squirrelmedia/X-TRACK/Software/X-Track/USER/App/Config/Config.h

/*
 * MIT License
 * Copyright (c) 2021 _VIFEXTech
 *
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
 * THE SOFTWARE IS PROVIDED "AS IS", WITHOUT WARRANTY OF ANY KIND, EXPRESS OR
 * IMPLIED, INCLUDING BUT NOT LIMITED TO THE WARRANTIES OF MERCHANTABILITY,
 * FITNESS FOR A PARTICULAR PURPOSE AND NONINFRINGEMENT. IN NO EVENT SHALL THE
 * AUTHORS OR COPYRIGHT HOLDERS BE LIABLE FOR ANY CLAIM, DAMAGES OR OTHER
 * LIABILITY, WHETHER IN AN ACTION OF CONTRACT, TORT OR OTHERWISE, ARISING FROM,
 * OUT OF OR IN CONNECTION WITH THE SOFTWARE OR THE USE OR OTHER DEALINGS IN THE
 * SOFTWARE.
 */
#ifndef __CONFIG_H
#define __CONFIG_H

/*=========================
   Application configuration
 *=========================*/

#define CONFIG_SYSTEM_SAVE_FILE_PATH          "/SystemSave.json"
#define CONFIG_SYSTEM_SAVE_FILE_BACKUP_PATH   "/.SystemSaveBackup.json"
#define CONFIG_SYSTEM_LANGUAGE_DEFAULT        "en-GB"
#define CONFIG_SYSTEM_TIME_ZONE_DEFAULT       8    // GMT+ 8
#define CONFIG_SYSTEM_SOUND_ENABLE_DEFAULT    true

#define CONFIG_WEIGHT_DEFAULT                 65   // kg

#ifdef ARDUINO
#  define CONFIG_GPS_REFR_PERIOD              1000 // ms
#else
#  define CONFIG_GPS_REFR_PERIOD              10 // ms
#endif

#define CONFIG_GPS_LONGITUDE_DEFAULT          116.391332f
#define CONFIG_GPS_LATITUDE_DEFAULT           39.907415f

#define CONFIG_TRACK_FILTER_OFFSET_THRESHOLD  2 // pixel
#define CONFIG_TRACK_RECORD_FILE_DIR_NAME     "Track"

#define CONFIG_MAP_USE_WGS84_DEFAULT          false
#define CONFIG_MAP_DIR_PATH_DEFAULT           "/MAP"

#define CONFIG_MAP_EXT_NAME_DEFAULT           "bin"

#ifndef CONFIG_MAP_IMG_PNG_ENABLE
#  define CONFIG_MAP_IMG_PNG_ENABLE           0
#endif

#define CONFIG_ARROW_THEME_DEFAULT            "default"

#define CONFIG_LIVE_MAP_LEVEL_DEFAULT         16

#define CONFIG_LIVE_MAP_DEBUG_ENABLE          0
#if CONFIG_LIVE_MAP_DEBUG_ENABLE
#  define CONFIG_LIVE_MAP_VIEW_WIDTH          240
#  define CONFIG_LIVE_MAP_VIEW_HEIGHT         240
#else
#  define CONFIG_LIVE_MAP_VIEW_WIDTH          LV_HOR_RES
#  define CONFIG_LIVE_MAP_VIEW_HEIGHT         LV_VER_RES
#endif

#define CONFIG_MONKEY_TEST_ENABLE             0
#if CONFIG_MONKEY_TEST_ENABLE
#  define CONFIG_MONKEY_INDEV_TYPE            LV_INDEV_TYPE_ENCODER
#  define CONFIG_MONKEY_PERIOD_MIN            10
#  define CONFIG_MONKEY_PERIOD_MAX            100
#  define CONFIG_MONKEY_INPUT_RANGE_MIN       -5
#  define CONFIG_MONKEY_INPUT_RANGE_MAX       5
#endif

#endif
