squirrelmedia/X-TRACK/Software/X-Track/MDK-ARM_F403A/Platform/Core/HardwareSerial.h

/*
 * MIT License
 * Copyright (c) 2019 _VIFEXTech
 *
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
 * THE SOFTWARE IS PROVIDED "AS IS", WITHOUT WARRANTY OF ANY KIND, EXPRESS OR
 * IMPLIED, INCLUDING BUT NOT LIMITED TO THE WARRANTIES OF MERCHANTABILITY,
 * FITNESS FOR A PARTICULAR PURPOSE AND NONINFRINGEMENT. IN NO EVENT SHALL THE
 * AUTHORS OR COPYRIGHT HOLDERS BE LIABLE FOR ANY CLAIM, DAMAGES OR OTHER
 * LIABILITY, WHETHER IN AN ACTION OF CONTRACT, TORT OR OTHERWISE, ARISING FROM,
 * OUT OF OR IN CONNECTION WITH THE SOFTWARE OR THE USE OR OTHER DEALINGS IN THE
 * SOFTWARE.
 */
#ifndef __HardwareSerial_h
#define __HardwareSerial_h

#include "Arduino.h"
#include "Print.h"
#include "Stream.h"

typedef enum
{
    SERIAL_8N1 = USART_WordLength_8b | USART_Parity_No | (USART_StopBits_1 >> 8),
    SERIAL_8N2 = USART_WordLength_8b | USART_Parity_No | (USART_StopBits_2 >> 8),
    SERIAL_8E1 = USART_WordLength_8b | USART_Parity_Even | (USART_StopBits_1 >> 8),
    SERIAL_8E2 = USART_WordLength_8b | USART_Parity_Even | (USART_StopBits_2 >> 8),
    SERIAL_8O1 = USART_WordLength_8b | USART_Parity_Odd | (USART_StopBits_1 >> 8),
    SERIAL_8O2 = USART_WordLength_8b | USART_Parity_Odd | (USART_StopBits_2 >> 8),
    SERIAL_8N0_5 = USART_WordLength_8b | USART_Parity_No | (USART_StopBits_0_5 >> 8),
    SERIAL_8N1_5 = USART_WordLength_8b | USART_Parity_No | (USART_StopBits_1_5 >> 8),
    SERIAL_8E0_5 = USART_WordLength_8b | USART_Parity_Even | (USART_StopBits_0_5 >> 8),
    SERIAL_8E1_5 = USART_WordLength_8b | USART_Parity_Even | (USART_StopBits_1_5 >> 8),
    SERIAL_8O0_5 = USART_WordLength_8b | USART_Parity_Odd | (USART_StopBits_0_5 >> 8),
    SERIAL_8O1_5 = USART_WordLength_8b | USART_Parity_Odd | (USART_StopBits_1_5 >> 8),

    SERIAL_9N1 = USART_WordLength_9b | USART_Parity_No | (USART_StopBits_1 >> 8),
    SERIAL_9N2 = USART_WordLength_9b | USART_Parity_No | (USART_StopBits_2 >> 8),
    SERIAL_9E1 = USART_WordLength_9b | USART_Parity_Even | (USART_StopBits_1 >> 8),
    SERIAL_9E2 = USART_WordLength_9b | USART_Parity_Even | (USART_StopBits_2 >> 8),
    SERIAL_9O1 = USART_WordLength_9b | USART_Parity_Odd | (USART_StopBits_1 >> 8),
    SERIAL_9O2 = USART_WordLength_9b | USART_Parity_Odd | (USART_StopBits_2 >> 8),
    SERIAL_9N0_5 = USART_WordLength_9b | USART_Parity_No | (USART_StopBits_0_5 >> 8),
    SERIAL_9N1_5 = USART_WordLength_9b | USART_Parity_No | (USART_StopBits_1_5 >> 8),
    SERIAL_9E0_5 = USART_WordLength_9b | USART_Parity_Even | (USART_StopBits_0_5 >> 8),
    SERIAL_9E1_5 = USART_WordLength_9b | USART_Parity_Even | (USART_StopBits_1_5 >> 8),
    SERIAL_9O0_5 = USART_WordLength_9b | USART_Parity_Odd | (USART_StopBits_0_5 >> 8),
    SERIAL_9O1_5 = USART_WordLength_9b | USART_Parity_Odd | (USART_StopBits_1_5 >> 8),
} SERIAL_Config_t;

class HardwareSerial : public Stream
{
    typedef void(*CallbackFunction_t)(HardwareSerial* serial);

public:
    HardwareSerial(USART_Type* usart);

    USART_Type* getUSART()
    {
        return _USARTx;
    }

    void begin(
        uint32_t baudRate,
        SERIAL_Config_t config = SERIAL_CONFIG_DEFAULT,
        uint8_t preemptionPriority = SERIAL_PREEMPTIONPRIORITY_DEFAULT,
        uint8_t subPriority = SERIAL_SUBPRIORITY_DEFAULT
    );
    void end(void);
    void attachInterrupt(CallbackFunction_t func);
    virtual int available(void);
    virtual int peek(void);
    virtual int read(void);
    virtual void flush(void);

    virtual size_t write(uint8_t n);
    inline size_t write(unsigned long n)
    {
        return write((uint8_t)n);
    }
    inline size_t write(long n)
    {
        return write((uint8_t)n);
    }
    inline size_t write(unsigned int n)
    {
        return write((uint8_t)n);
    }
    inline size_t write(int n)
    {
        return write((uint8_t)n);
    }
    using Print::write; // pull in write(str) and write(buf, size) from Print
    operator bool()
    {
        return true;
    }

    void IRQHandler();

private:
    USART_Type* _USARTx;
    CallbackFunction_t _callbackFunction;
    volatile uint16_t _rxBufferHead;
    volatile uint16_t _rxBufferTail;
    uint8_t _rxBuffer[SERIAL_RX_BUFFER_SIZE];
};

#if SERIAL_1_ENABLE
extern HardwareSerial Serial;
#endif

#if SERIAL_2_ENABLE
extern HardwareSerial Serial2;
#endif

#if SERIAL_3_ENABLE
extern HardwareSerial Serial3;
#endif

#endif
