squirrelmedia/X-TRACK/Software/X-Track/Linux/mouse_cursor_icon.c

#include "lvgl/lvgl.h"

const uint8_t mouse_cursor_icon_map[] = {
#if LV_COLOR_DEPTH == 1 || LV_COLOR_DEPTH == 8
    /*Pixel format: Alpha 8 bit, Red: 3 bit, Green: 3 bit, Blue: 2 bit*/
    0x24, 0xb8, 0x24, 0xc8, 0x00, 0x13, 0x00, 0x00, 0x00, 0x03, 0x00, 0x00, 0x00, 0x00, 0x00, 0x00, 0x00, 0x00, 0x00, 0x00, 0x00, 0x00, 0x00, 0x00, 0x00, 0x00, 0x00, 0x00,
    0x49, 0xcc, 0xdb, 0xff, 0x49, 0xcc, 0x00, 0x24, 0x00, 0x00, 0x00, 0x00, 0x00, 0x00, 0x00, 0x00, 0x00, 0x00, 0x00, 0x00, 0x00, 0x00, 0x00, 0x00, 0x00, 0x00, 0x00, 0x00,
    0x49, 0xc8, 0xff, 0xff, 0xff, 0xff, 0x49, 0xe0, 0x00, 0x3b, 0x00, 0x00, 0x00, 0x00, 0x00, 0x00, 0x00, 0x00, 0x00, 0x00, 0x00, 0x00, 0x00, 0x00, 0x00, 0x00, 0x00, 0x00,
    0x49, 0xcb, 0xff, 0xff, 0xff, 0xfc, 0xff, 0xff, 0x6d, 0xf3, 0x00, 0x4f, 0x00, 0x00, 0x00, 0x00, 0x00, 0x00, 0x00, 0x00, 0x00, 0x00, 0x00, 0x00, 0x00, 0x00, 0x00, 0x00,
    0x49, 0xcb, 0xff, 0xff, 0xff, 0xff, 0xff, 0xff, 0xff, 0xff, 0x92, 0xff, 0x00, 0x73, 0x00, 0x00, 0x00, 0x00, 0x00, 0x03, 0x00, 0x00, 0x00, 0x00, 0x00, 0x00, 0x00, 0x00,
    0x49, 0xcb, 0xff, 0xff, 0xff, 0xff, 0xff, 0xff, 0xff, 0xff, 0xff, 0xff, 0x92, 0xff, 0x00, 0x90, 0x00, 0x00, 0x00, 0x00, 0xb6, 0x00, 0x00, 0x00, 0x00, 0x00, 0x00, 0x00,
    0x49, 0xcb, 0xff, 0xff, 0xff, 0xff, 0xff, 0xff, 0xff, 0xff, 0xff, 0xff, 0xff, 0xff, 0xb7, 0xff, 0x24, 0xab, 0x00, 0x04, 0x00, 0x00, 0x00, 0x00, 0x00, 0x00, 0x00, 0x00,
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
#endif
};

lv_img_dsc_t mouse_cursor_icon = {
    .header.always_zero = 0,
    .header.w = 14,
    .header.h = 20,
    .data_size = 280 * LV_IMG_PX_SIZE_ALPHA_BYTE,
    .header.cf = LV_IMG_CF_TRUE_COLOR_ALPHA,
    .data = mouse_cursor_icon_map,
};
