squirrelmedia/X-TRACK/Software/X-Track/MDK-ARM_F403A/Platform/Core/SPI.h

/*
 * MIT License
 * Copyright (c) 2017 - 2022 _VIFEXTech
 *
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
 * THE SOFTWARE IS PROVIDED "AS IS", WITHOUT WARRANTY OF ANY KIND, EXPRESS OR
 * IMPLIED, INCLUDING BUT NOT LIMITED TO THE WARRANTIES OF MERCHANTABILITY,
 * FITNESS FOR A PARTICULAR PURPOSE AND NONINFRINGEMENT. IN NO EVENT SHALL THE
 * AUTHORS OR COPYRIGHT HOLDERS BE LIABLE FOR ANY CLAIM, DAMAGES OR OTHER
 * LIABILITY, WHETHER IN AN ACTION OF CONTRACT, TORT OR OTHERWISE, ARISING FROM,
 * OUT OF OR IN CONNECTION WITH THE SOFTWARE OR THE USE OR OTHER DEALINGS IN THE
 * SOFTWARE.
 */
#ifndef __SPI_H
#define __SPI_H

#include "Arduino.h"

#ifndef LSBFIRST
#  define LSBFIRST 0
#endif
#ifndef MSBFIRST
#  define MSBFIRST 1
#endif

#if SPI_CLASS_PIN_DEFINE_ENABLE
#  define SS      PA4
#  define SCK     PA5
#  define MISO    PA6
#  define MOSI    PA7
#endif

#define DATA_SIZE_8BIT  SPI_FRAMESIZE_8BIT
#define DATA_SIZE_16BIT SPI_FRAMESIZE_16BIT

#define SPI_I2S_GET_FLAG(spix, SPI_I2S_FLAG) (spix->STS & SPI_I2S_FLAG)
#define SPI_I2S_RXDATA(spix)                 (spix->DT)
#define SPI_I2S_RXDATA_VOLATILE(spix)        volatile uint16_t vn = SPI_I2S_RXDATA(spix)
#define SPI_I2S_TXDATA(spix, data)           (spix->DT = (data))
#define SPI_I2S_WAIT_RX(spix)                do{ while (!SPI_I2S_GET_FLAG(spix, SPI_I2S_FLAG_RNE));  } while(0)
#define SPI_I2S_WAIT_TX(spix)                do{ while (!SPI_I2S_GET_FLAG(spix, SPI_STS_TE));        } while(0)
#define SPI_I2S_WAIT_BUSY(spix)              do{ while (SPI_I2S_GET_FLAG(spix,  SPI_I2S_FLAG_BUSY)); } while(0)

typedef enum
{
    SPI_MODE0,
    SPI_MODE1,
    SPI_MODE2,
    SPI_MODE3
} SPI_MODE_TypeDef;

typedef enum
{
    SPI_STATE_IDLE,
    SPI_STATE_READY,
    SPI_STATE_RECEIVE,
    SPI_STATE_TRANSMIT,
    SPI_STATE_TRANSFER
} spi_mode_t;

class SPISettings
{
public:
    SPISettings(uint32_t clock, uint16_t bitOrder, uint8_t dataMode)
    {
        init_AlwaysInline(clock, bitOrder, dataMode, DATA_SIZE_8BIT);
    }
    SPISettings(uint32_t clock, uint16_t bitOrder, uint8_t dataMode, uint32_t dataSize)
    {
        init_AlwaysInline(clock, bitOrder, dataMode, dataSize);
    }
    SPISettings(uint32_t clock)
    {
        init_AlwaysInline(clock, MSBFIRST, SPI_MODE0, DATA_SIZE_8BIT);
    }
    SPISettings()
    {
        init_AlwaysInline(4000000, MSBFIRST, SPI_MODE0, DATA_SIZE_8BIT);
    }
private:
    void init_MightInline(uint32_t clock, uint16_t bitOrder, uint8_t dataMode, uint32_t dataSize)
    {
        init_AlwaysInline(clock, bitOrder, dataMode, dataSize);
    }
    void init_AlwaysInline(uint32_t clock, uint16_t bitOrder, uint8_t dataMode, uint32_t dataSize) __attribute__((__always_inline__))
    {
        this->clock = clock;
        this->bitOrder = bitOrder;
        this->dataMode = dataMode;
        this->dataSize = dataSize;
    }
    uint32_t clock;
    uint32_t dataSize;
    uint16_t bitOrder;
    uint8_t dataMode;

    friend class SPIClass;
};

class SPIClass
{
public:
    SPIClass(SPI_Type* spix);

    SPI_Type* getSPI()
    {
        return SPIx;
    }

    void SPI_Settings(
        uint16_t SPI_Mode_x,
        uint16_t SPI_DataSize_x,
        uint16_t SPI_MODEx,
        uint16_t SPI_NSS_x,
        uint16_t SPI_BaudRatePrescaler_x,
        uint16_t SPI_FirstBit_x
    );
    void begin(void);
    void begin(uint32_t clock, uint16_t dataOrder, uint16_t dataMode);
    void begin(SPISettings settings);
    void beginSlave(uint32_t bitOrder, uint32_t mode);
    void beginSlave(void);
    void beginTransactionSlave(void);
    void beginTransaction(SPISettings settings);

    void endTransaction(void);
    void end(void);

    void setClock(uint32_t clock);
    void setClockDivider(uint32_t Div);
    void setBitOrder(uint16_t bitOrder);
    void setDataMode(uint8_t dataMode);
    void setDataSize(uint16_t datasize);

    uint16_t read(void);
    void read(uint8_t* buffer, uint32_t length);
    void write(uint16_t data);
    void write(uint16_t data, uint32_t n);
    void write(const uint8_t* data, uint32_t length);
    void write(const uint16_t* data, uint32_t length);
    uint8_t transfer(uint8_t data) const;
    uint16_t transfer16(uint16_t data) const;
    uint8_t send(uint8_t data);
    uint8_t send(uint8_t* data, uint32_t length);
    uint8_t recv(void);

private:
    SPI_Type* SPIx;
    SPI_InitType SPI_InitStructure;
    uint32_t SPI_Clock;
};

#if SPI_CLASS_1_ENABLE
extern SPIClass SPI;
#endif

#if SPI_CLASS_2_ENABLE
extern SPIClass SPI_2;
#endif

#if SPI_CLASS_3_ENABLE
extern SPIClass SPI_3;
#endif

#endif
