squirrelmedia/X-TRACK/Software/X-Track/MDK-ARM_F403A/Platform/Core/extend_SRAM.h

/**
  ******************************************************************************
  * File   : SRAM/extend_SRAM/EXTEND_SRAM/extend_SRAM.h
  * Version: V1.2.7
  * Date   : 2020-11-10
  * Brief  : This file contains all the macros used in extend_SRAM.c
  ******************************************************************************
  */

/* Define to prevent recursive inclusion -------------------------------------*/
#ifndef __EXTEND_SRAM_H
#define __EXTEND_SRAM_H

/* Exported functions ------------------------------------------------------- */
void extend_SRAM(void);

#endif /* __EXTEND_SRAM_H */
