squirrelmedia/X-TRACK/Software/X-Track/USER/HAL/HAL_FaultHandle.cpp

#include "HAL.h"
#include "App/Version.h"
#include "cm_backtrace/cm_backtrace.h"

static void Delay(uint32_t ms)
{
    volatile uint32_t i = F_CPU / 1000 * ms / 5;
    while(i--);
}

static void Reboot()
{
    while(digitalRead(CONFIG_ENCODER_PUSH_PIN) == HIGH)
    {
        Delay(1000);
    }
    NVIC_SystemReset();
}

void HAL::FaultHandle_Init()
{
    cm_backtrace_init(
        VERSION_FIRMWARE_NAME,
        VERSION_HARDWARE,
        VERSION_SOFTWARE " " __DATE__
    );
}

void cmb_printf(const char *__restrict __format, ...)
{
    char printf_buff[256];

    va_list args;
    va_start(args, __format);
    int ret_status = vsnprintf(printf_buff, sizeof(printf_buff), __format, args);
    va_end(args);
    
    Serial.print(printf_buff);
}

extern "C"
{
    /*
    void vApplicationStackOverflowHook(TaskHandle_t xTask, char* pcTaskName)
    {
        char strBuf[configMAX_TASK_NAME_LEN + 1];
        snprintf(strBuf, sizeof(strBuf), "stack overflow\n < %s >", pcTaskName);
        DisplayError_SetReports(strBuf);
        Reboot();
    }
    
    void vApplicationMallocFailedHook()
    {
        DisplayError_SetReports("malloc failed");
        Reboot();
    }
    */
    
    void vApplicationHardFaultHook()
    {
        HAL::Display_DumpCrashInfo("FXXK HardFault!");
        Reboot();
    }
    
    __asm void HardFault_Handler()
    {
        extern vApplicationHardFaultHook
        extern cm_backtrace_fault
            
        mov r0, lr
        mov r1, sp
        bl cm_backtrace_fault
        bl vApplicationHardFaultHook
fault_loop
        b fault_loop
    }
}
